myriadrf/LimeSDR-Mini-v2/hardware/2v4/Project Outputs for LimeSDR-Mini_2v4/ERC/LimeSDR-Mini_2v4.html

Altium

# Electrical Rule Check Report

Date: | | 2023-04-24
Time: | | 16:05:35
Filename: | | E:\Saniok\Lime Micro\Lime PCBs\LimeSDR_Mini\LimeSDR_Mini_2v4\Altium Designer design files\Project Outputs for LimeSDR-Mini_2v4\ERC\LimeSDR-Mini_2v4.html

Class | Document | Message

Warning

10_Misc.SchDoc

GND contains IO Pin and Power Pin objects (Pin IC12-4,Pin IC2-4,Pin IC11-5,Pin IC19-6,Pin IC14-6,Pin IC7-B3,Pin IC7-B16,Pin IC7-E5,Pin IC7-E7,Pin IC7-E8,Pin IC7-E9,Pin IC7-E10,Pin IC7-E11,Pin IC7-E12,Pin IC7-E14,Pin IC7-F5,Pin IC7-F6,Pin IC7-F7,Pin IC7-F8,Pin IC7-F9,Pin IC7-F10,Pin IC7-F11,Pin IC7-F12,Pin IC7-F13,Pin IC7-F14,Pin IC7-G2,Pin IC7-G6,Pin IC7-G7,Pin IC7-G8,Pin IC7-G9,Pin IC7-G10,Pin IC7-G11,Pin IC7-G12,Pin IC7-G13,Pin IC7-G17,Pin IC7-H6,Pin IC7-H7,Pin IC7-H8,Pin IC7-H9,Pin IC7-H10,Pin IC7-H11,Pin IC7-H12,Pin IC7-H13,Pin IC7-J3,Pin IC7-J6,Pin IC7-J7,Pin IC7-J8,Pin IC7-J9,Pin IC7-J10,Pin IC7-J11,Pin IC7-J12,Pin IC7-J13,Pin IC7-K5,Pin IC7-K6,Pin IC7-K7,Pin IC7-K8,Pin IC7-K9,Pin IC7-K10,Pin IC7-K11,Pin IC7-K12,Pin IC7-K13,Pin IC7-K14,Pin IC7-L2,Pin IC7-L5,Pin IC7-L6,Pin IC7-L7,Pin IC7-L8,Pin IC7-L9,Pin IC7-L10,Pin IC7-L11,Pin IC7-L12,Pin IC7-L13,Pin IC7-L14,Pin IC7-L17,Pin IC7-M6,Pin IC7-M7,Pin IC7-M8,Pin IC7-M9,Pin IC7-M10,Pin IC7-M11,Pin IC7-M12,Pin IC7-M13,Pin IC7-N7,Pin IC7-N8,Pin IC7-N9,Pin IC7-N10,Pin IC7-N11,Pin IC7-N12,Pin IC7-P5,Pin IC7-P6,Pin IC7-P8,Pin IC7-P10,Pin IC7-P12,Pin IC12-PAD,Pin IC2-PAD,Pin IC7-R1,Pin IC7-R2,Pin IC7-R3,Pin IC7-R10,Pin IC7-T1,Pin IC7-T2,Pin IC7-T3,Pin IC7-T4,Pin IC7-T5,Pin IC7-T6,Pin IC7-T7,Pin IC7-T8,Pin IC7-T9,Pin IC7-T10,Pin IC7-T11,Pin IC7-T12,Pin IC7-T16,Pin IC7-U1,Pin IC7-U2,Pin IC7-U3,Pin IC7-U4,Pin IC7-U5,Pin IC7-U6,Pin IC7-U7,Pin IC7-U8,Pin IC7-U9,Pin IC7-U10,Pin IC7-U11,Pin IC7-U12,Pin IC7-U14,Pin IC7-V4,Pin IC7-V5,Pin IC7-V6,Pin IC7-V7,Pin IC7-V8,Pin IC7-V9,Pin IC7-V10,Pin IC7-V15)
Warning | 10_Misc.SchDoc | Net EN_VCC3P3 has no driving source (Pin C194-2,Pin IC19-2,Pin R86-1,Pin R90-2,Pin R93-1)
Warning | 05_LMS7002M_Misc.SchDoc | Net LMS_I2C_SCL has no driving source (Pin IC1-C27,Pin IC2-6,Pin R2-2)
Warning | 07_LMS7002M_Power.SchDoc | Net NetC68_2 has no driving source (Pin C68-2,Pin FR22-2,Pin IC5-1,Pin IC5-6)
Warning | 07_LMS7002M_Power.SchDoc | Net NetC82_2 has no driving source (Pin C82-2,Pin FR25-2,Pin IC6-1,Pin IC6-6)
Warning | 10_Misc.SchDoc | Net NetC157_2 has no driving source (Pin C157-2,Pin XO1-7)
Warning | 10_Misc.SchDoc | Net NetC182_2 has no driving source (Pin C182-2,Pin IC14-4,Pin R79-1,Pin R82-2)
Warning | 10_Misc.SchDoc | Net NetC193_2 has no driving source (Pin C193-2,Pin IC19-4,Pin R88-1,Pin R91-2)
Warning | 07_LMS7002M_Power.SchDoc | Net NetIC5_5 has no driving source (Pin IC5-5,Pin R31-1,Pin R33-2)
Warning | 07_LMS7002M_Power.SchDoc | Net NetIC6_5 has no driving source (Pin IC6-5,Pin R38-1,Pin R39-2)
Warning | 10_Misc.SchDoc | Net NetIC13_5 has no driving source (Pin IC13-5,Pin R74-1,Pin R80-1)
Warning | 10_Misc.SchDoc | Net NetIC18_5 has no driving source (Pin IC18-5,Pin R84-1,Pin R89-1)
Warning | 10_Misc.SchDoc | Net TCXO_DAC_VREF has no driving source (Pin C183-1,Pin IC16-2,Pin R76-1,Pin R78-2,Pin R81-1,Pin R83-1)
Warning | 09_USB3_0_FIFO.SchDoc | Net USB_SSRX_N has no driving source (Pin ESD3-7,Pin IC8-34,Pin J6-8)
Warning | 09_USB3_0_FIFO.SchDoc | Net USB_SSRX_P has no driving source (Pin ESD3-8,Pin IC8-35,Pin J6-9)
Warning | 10_Misc.SchDoc | VCC3P3 contains IO Pin and Output Pin objects (Pin IC19-5,Pin IC7-T14)
Warning | 10_Misc.SchDoc | VCC3P3 contains IO Pin and Power Pin objects (Pin LED3-1,Pin LED2-1,Pin LED1-1,Pin LED3-2,Pin LED2-2,Pin LED1-2,Pin IC12-8,Pin IC7-D7,Pin IC7-D12,Pin IC7-G14,Pin IC7-H14,Pin IC7-M14,Pin IC7-N13,Pin IC7-N14,Pin IC7-P14,Pin IC7-T14)

Back to top
