myriadrf/LimeSDR-Mini-v2/hardware/2v0/Project Outputs for LimeSDR_Mini_2v0/DRC/LimeSDR_Mini_2v0_Rounded.html

Altium

# Design Rule Verification Report

Date: | | 2021-12-01
Time: | | 10:46:40
Elapsed Time: | | 00:00:43
Filename: | | E:\Saniok\Lime Micro\Lime PCBs\LimeSDR_Mini_2v0\Altium designer design files\PCB\LimeSDR_Mini_2v0_Rounded.PcbDoc

Warnings: | | 0
Rule Violations: | | 0

## Summary

Warnings | Count
Total | 0

Rule Violations | Count
Clearance Constraint (Gap=0.1mm) (All),(All) | 0
Clearance Constraint (Gap=0.076mm) (WithinRoom('FPGA_fanout')),(All) | 0
Short-Circuit Constraint (Allowed=No) (All),(All) | 0
Un-Routed Net Constraint ( (All) ) | 0
Modified Polygon (Allow modified: No), (Allow shelved: No) | 0
Width Constraint (Min=0.1mm) (Max=7mm) (Preferred=0.2mm) (All) | 0
Width Constraint (Min=0.076mm) (Max=5mm) (Preferred=0.127mm) (WithinRoom('FPGA_fanout')) | 0
Width Constraint (Min=0.1mm) (Max=5mm) (Preferred=0.2mm) (All) | 0
Routing Layers(All) | 0
Routing Via (MinHoleWidth=0.15mm) (MaxHoleWidth=4.5mm) (PreferredHoleWidth=0.2mm) (MinWidth=0.3mm) (MaxWidth=5mm) (PreferedWidth=0.4mm) (All) | 0
Differential Pairs Uncoupled Length using the Gap Constraints (Min=0.14mm) (Max=0.14mm) (Prefered=0.14mm) and Width Constraints (Min=0.1mm) (Max=0.2mm) (Prefered=0.2mm) (InNetClass('TX_RF')) | 0
Differential Pairs Uncoupled Length using the Gap Constraints (Min=0.1mm) (Max=0.3mm) (Prefered=0.14mm) and Width Constraints (Min=0.1mm) (Max=0.3mm) (Prefered=0.2mm) (InNetClass('RX_RF')) | 0
Differential Pairs Uncoupled Length using the Gap Constraints (Min=0.1mm) (Max=0.2mm) (Prefered=0.1mm) and Width Constraints (Min=0.1mm) (Max=0.4mm) (Prefered=0.1mm) (InNet('FX3_XTAL_N') or InNet('FX3_XTAL_P')) | 0
Differential Pairs Uncoupled Length using the Gap Constraints (Min=0.1mm) (Max=0.3mm) (Prefered=0.1mm) and Width Constraints (Min=0.1mm) (Max=0.5mm) (Prefered=0.2mm) (All) | 0
Differential Pairs Uncoupled Length using the Gap Constraints (Min=0.1mm) (Max=0.3mm) (Prefered=0.14mm) and Width Constraints (Min=0.2mm) (Max=0.2mm) (Prefered=0.2mm) (InNetClass('FX3_DATA')) | 0
Power Plane Connect Rule(Relief Connect )(Expansion=0.508mm) (Conductor Width=0.254mm) (Air Gap=0.254mm) (Entries=4) (All) | 0
Hole Size Constraint (Min=0.15mm) (Max=10mm) (All) | 0
Pads and Vias to follow the Drill pairs settings | 0
Hole To Hole Clearance (Gap=0.15mm) (All),(All) | 0
Minimum Solder Mask Sliver (Gap=0.05mm) (All),(All) | 0
Net Antennae (Tolerance=0mm) (All) | 0
Matched Lengths(Tolerance=5mm) (InNetClass('FT_FIFO')) | 0
Matched Lengths(Tolerance=7.5mm) (InNetClass('LMS_PORT2')) | 0
Matched Lengths(Tolerance=7mm) (InNetClass('LMS_PORT1')) | 0
Component Clearance Constraint ( Horizontal Gap = 0.01mm, Vertical Gap = 0.254mm ) (All),(All) | 0
Component Clearance Constraint ( Horizontal Gap = -1mm, Vertical Gap = Infinite ) (InComponent('IC11') or InComponent('IC11A')),(InComponent('IC11') or InComponent('IC11A')) | 0
Component Clearance Constraint ( Horizontal Gap = -1mm, Vertical Gap = Infinite ) (InComponent('R63') or InComponent('R66')),(InComponent('R63') or InComponent('R66')) | 0
Component Clearance Constraint ( Horizontal Gap = -1mm, Vertical Gap = Infinite ) (InComponent('R28') or InComponent('C22') or InComponent('R29') or InComponent('C20')),(InComponent('R28') or InComponent('C22') or InComponent('R29') or InComponent('C20')) | 0
Component Clearance Constraint ( Horizontal Gap = -10mm, Vertical Gap = Infinite ) (InComponent('MECH1') or InComponent('MECH2') or InComponent('MECH3') or InComponent('MECH4') or InComponent('MECH5') or InComponent('MECH12') or InComponent('MECH13') or InComponent('MECH14') or InComponent('MECH15') or InComponent('MECH16') or InComponent('J3') or InComponent('MECH17') or InComponent('MECH18') or InComponent('MECH19') or InComponent('MECH20') or InComponent('MECH21')),(All) | 0
Height Constraint (Min=0mm) (Max=25.4mm) (Prefered=12.7mm) (All) | 0
Total | 0
