myriadrf/LimeSDR-Mini-v2/docs/documentation/images/image_2023_01_11T06_07_56_163Z.png

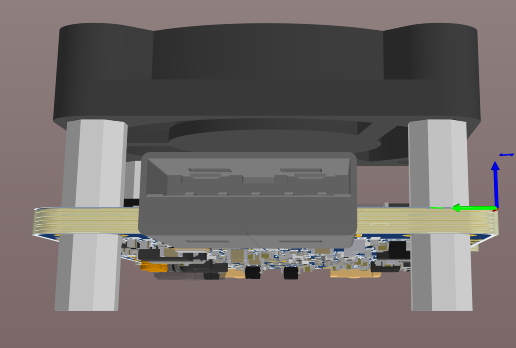
docs/documentation/images/image_2023_01_11T06_07_56_163Z.png
