myriadrf/LimeSDR-Mini-v2/docs/documentation/images/image_2023_01_11T08_47_21_025Z.png

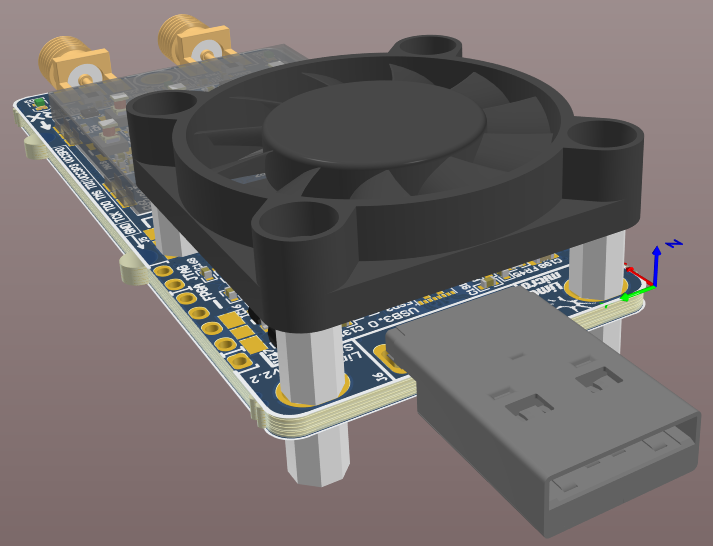
docs/documentation/images/image_2023_01_11T08_47_21_025Z.png
