myriadrf/LimeSDR-Mini-v2/hardware/2v2/Project Outputs/LimeSDR-Mini_2v1_PCBspecs_r0.PDF

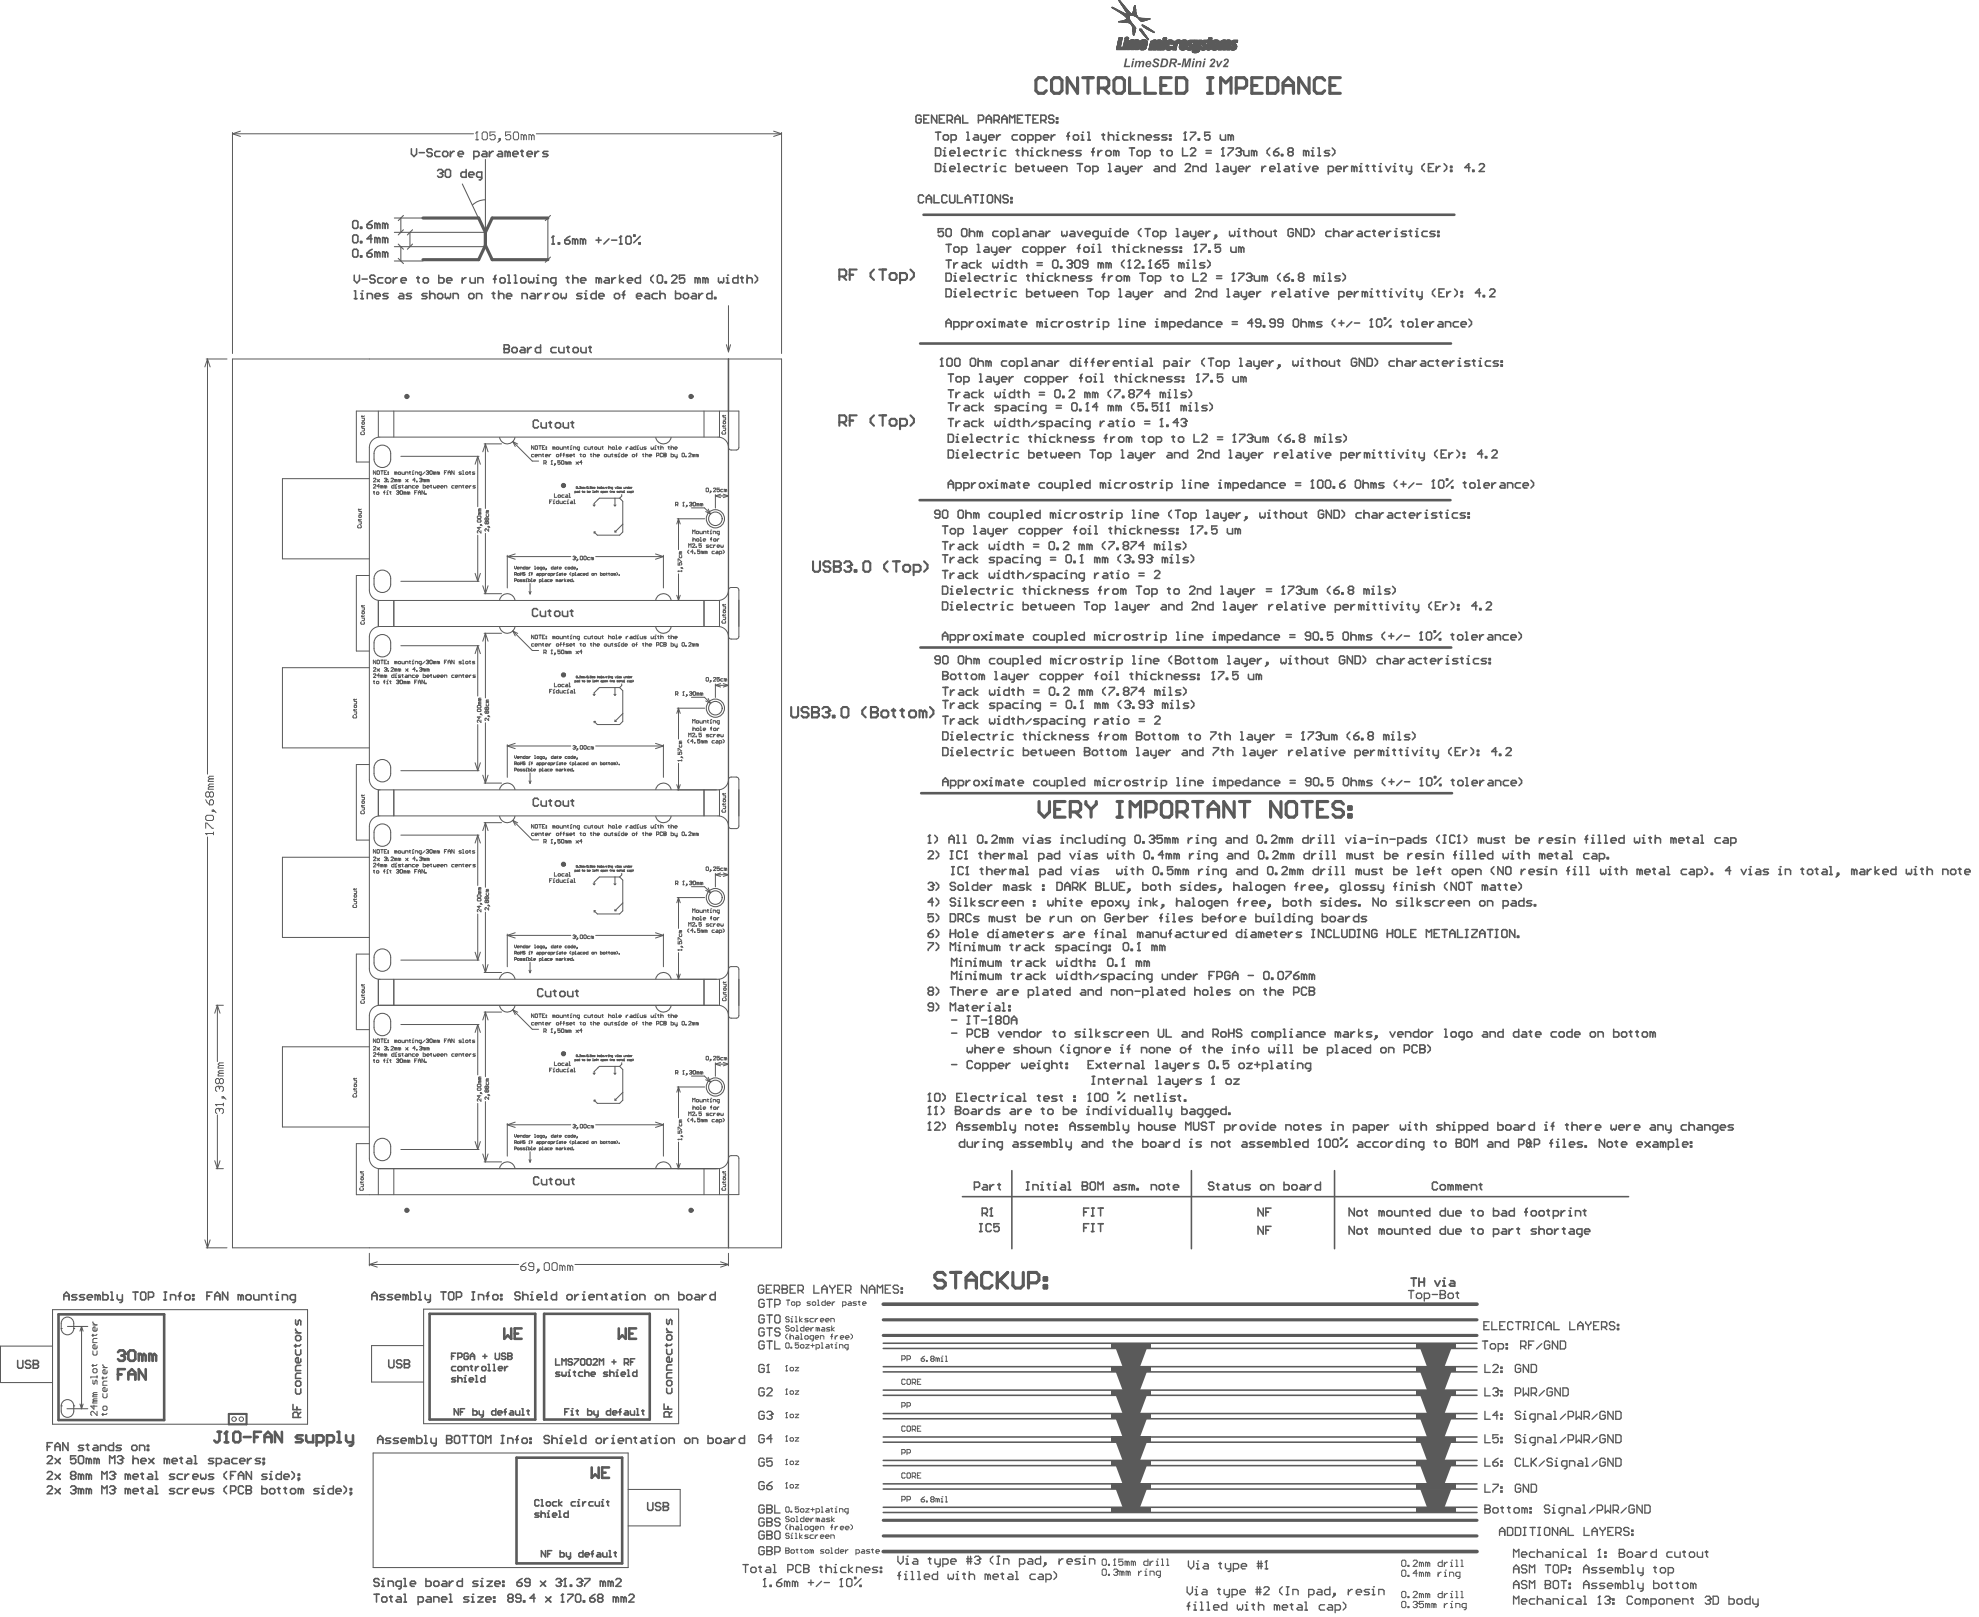
[picture p55: page 1]
