myriadrf/LimeSDR-Mini-v2/hardware/2v2/Project Outputs/LimeSDR-Mini_2v2_PCB_Drawings_r0.PDF

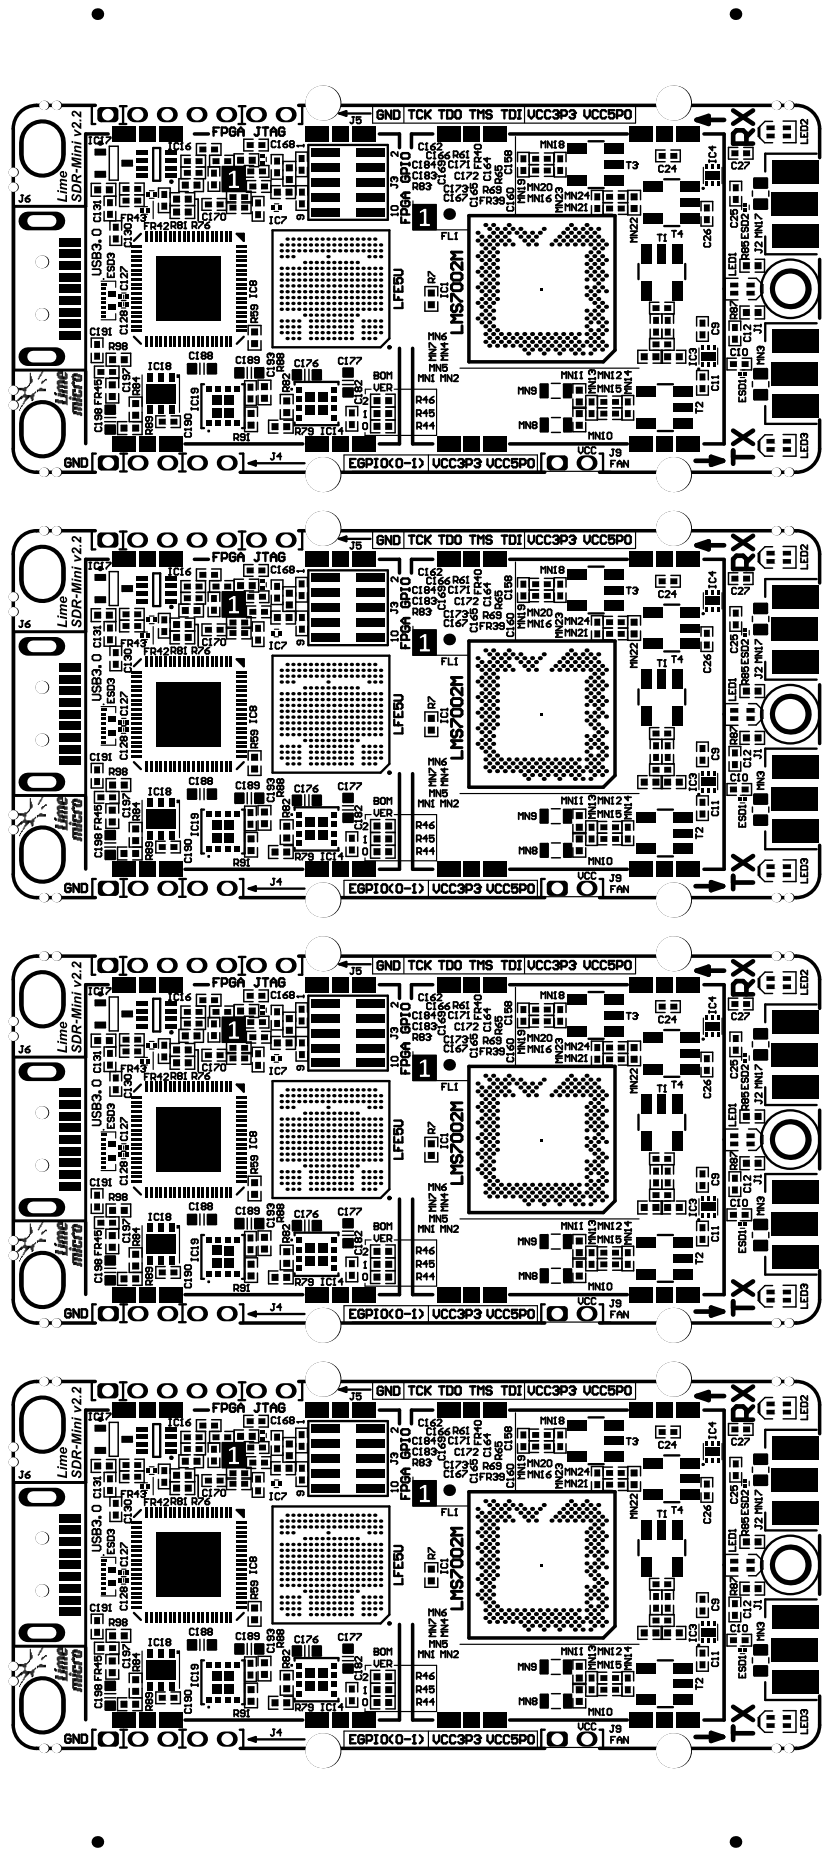
[picture p56: page 1]

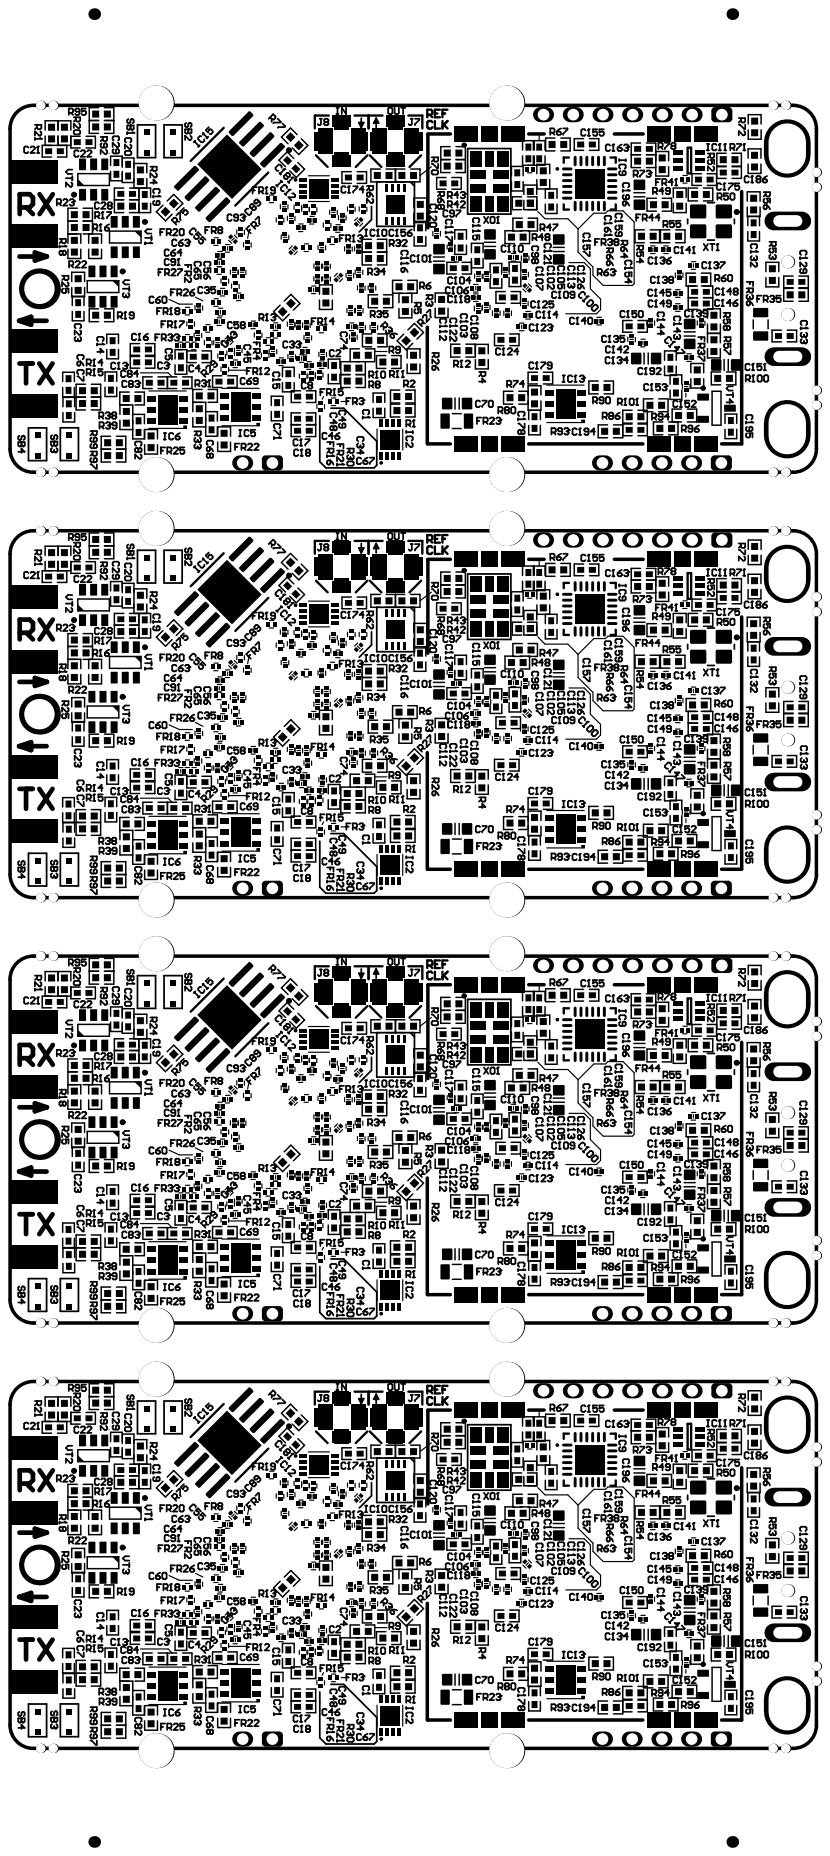
[picture p57: page 2]
