myriadrf/LimeSDR-Mini-v2/hardware/2v2/Project Outputs/LimeSDR-Mini_2v2_Single_Brd_Assembly_Drawings_r0.PDF

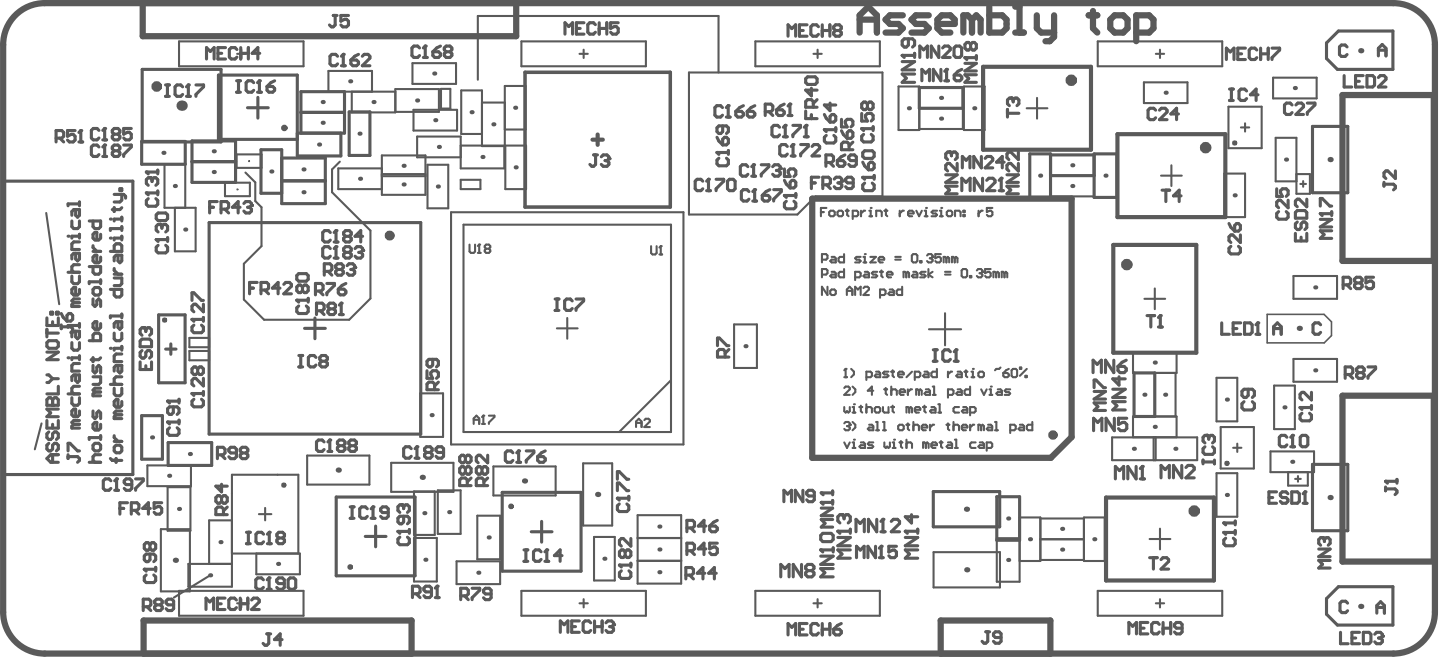
[picture p58: page 1]

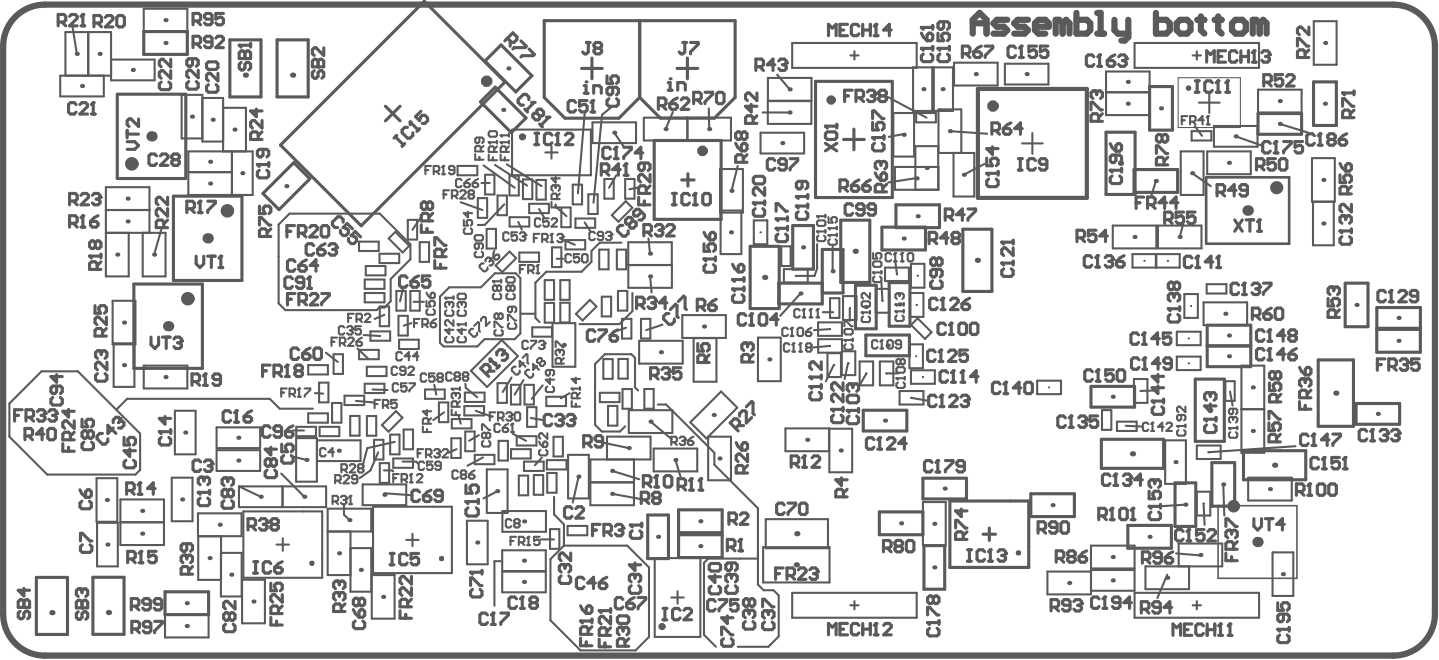
[picture p59: page 2]
